amargandhi/claude-buddy-pico/docs/assets/pico-ble-smoke.jpeg

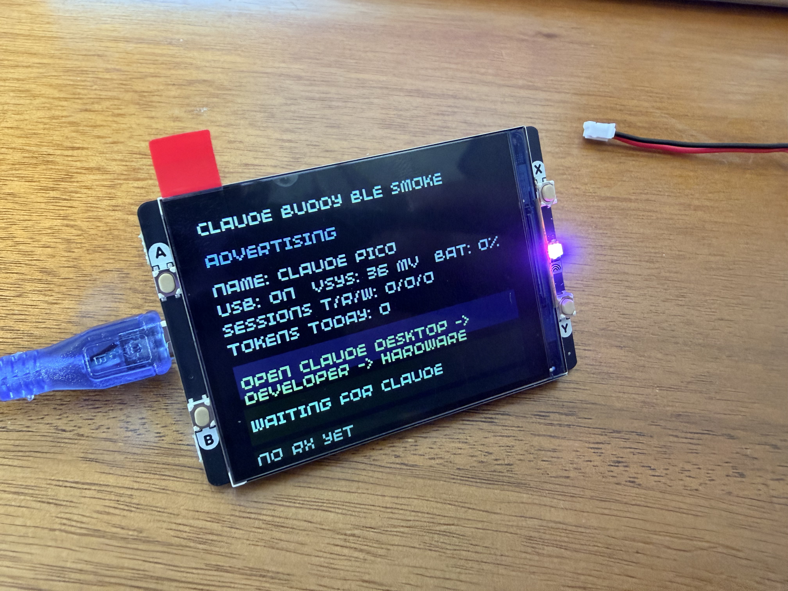
docs/assets/pico-ble-smoke.jpeg
