amargandhi/claude-buddy-pico/docs/assets/readme-gallery-left.jpg

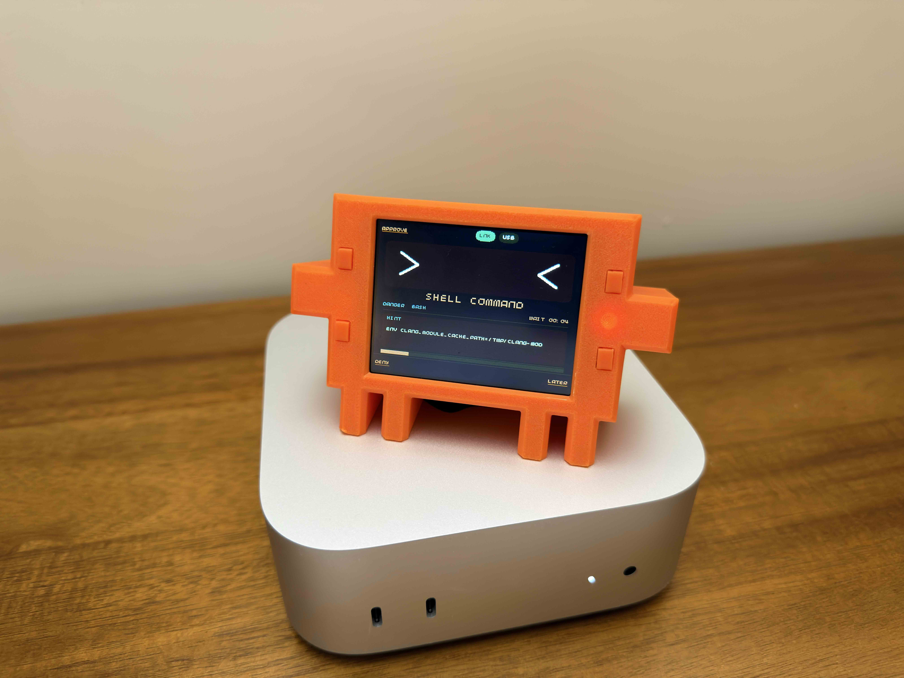
docs/assets/readme-gallery-left.jpg
