amargandhi/claude-buddy-pico/Physical Build/Photos_web/01_hardware/01_02_pico_2w_top.jpg

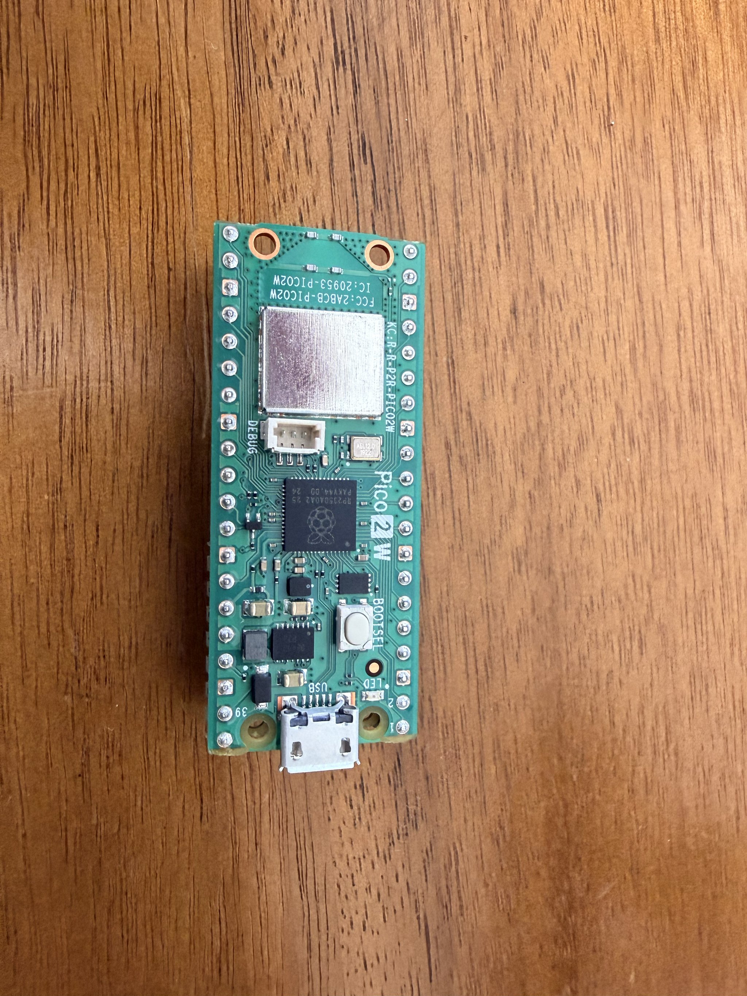
Physical Build/Photos_web/01_hardware/01_02_pico_2w_top.jpg
