amargandhi/claude-buddy-pico/Physical Build/Photos_web/01_hardware/01_04_pico_shim_stack_side.jpg

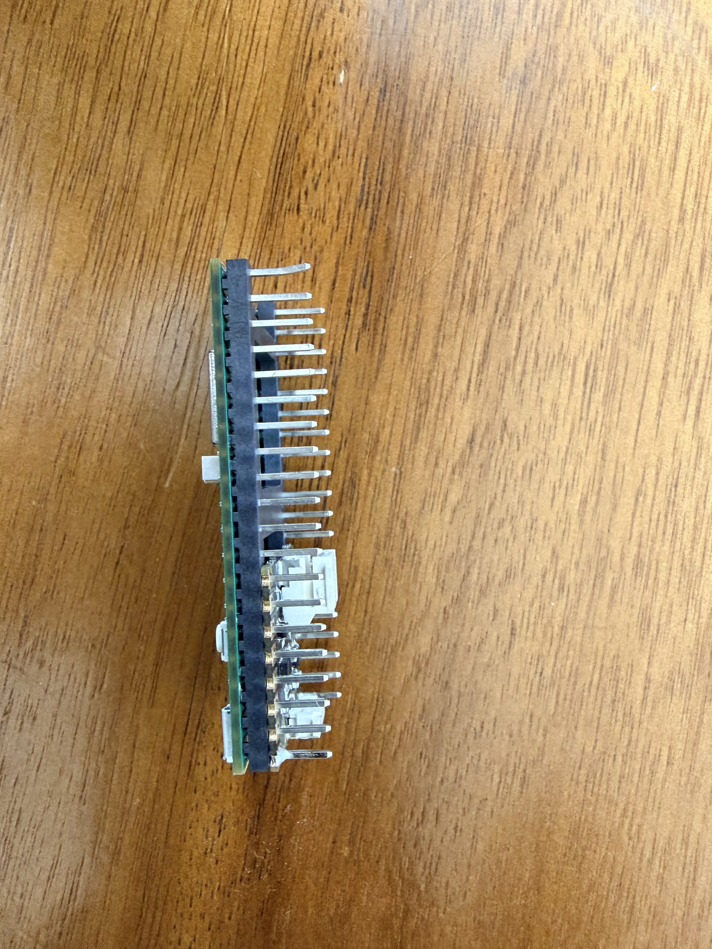
Physical Build/Photos_web/01_hardware/01_04_pico_shim_stack_side.jpg
