amargandhi/claude-buddy-pico/Physical Build/Photos_web/01_hardware/01_06_parts_layout_a.jpg

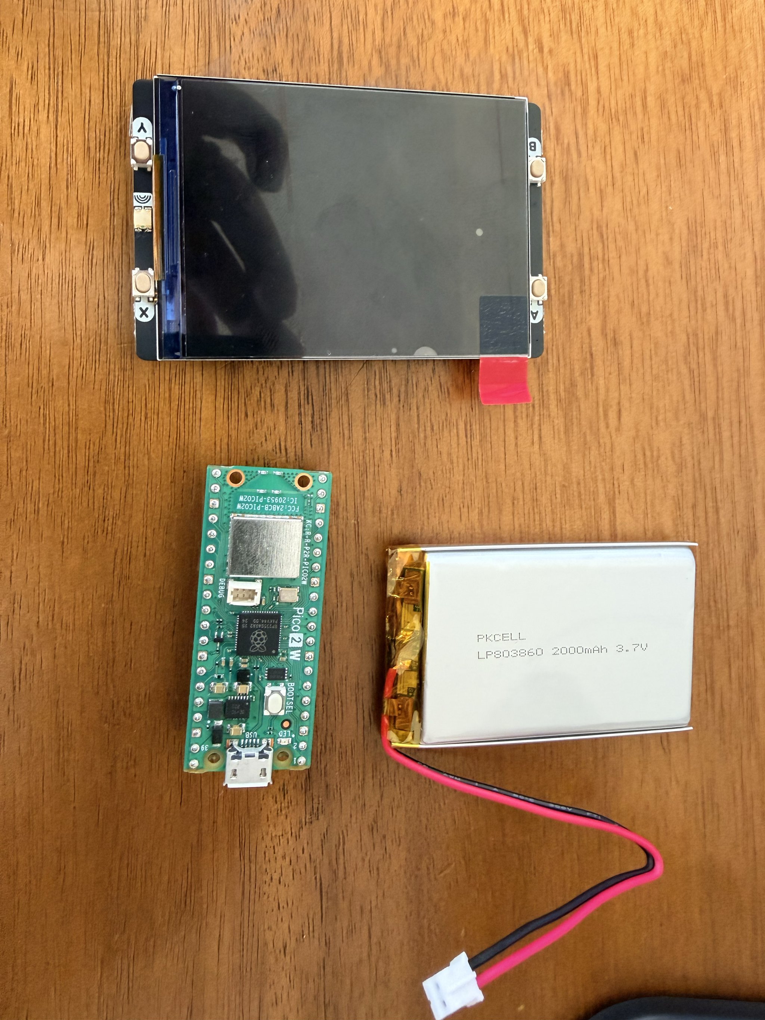
Physical Build/Photos_web/01_hardware/01_06_parts_layout_a.jpg
