amargandhi/claude-buddy-pico/Physical Build/Photos_web/01_hardware/01_08_parts_layout_c.jpg

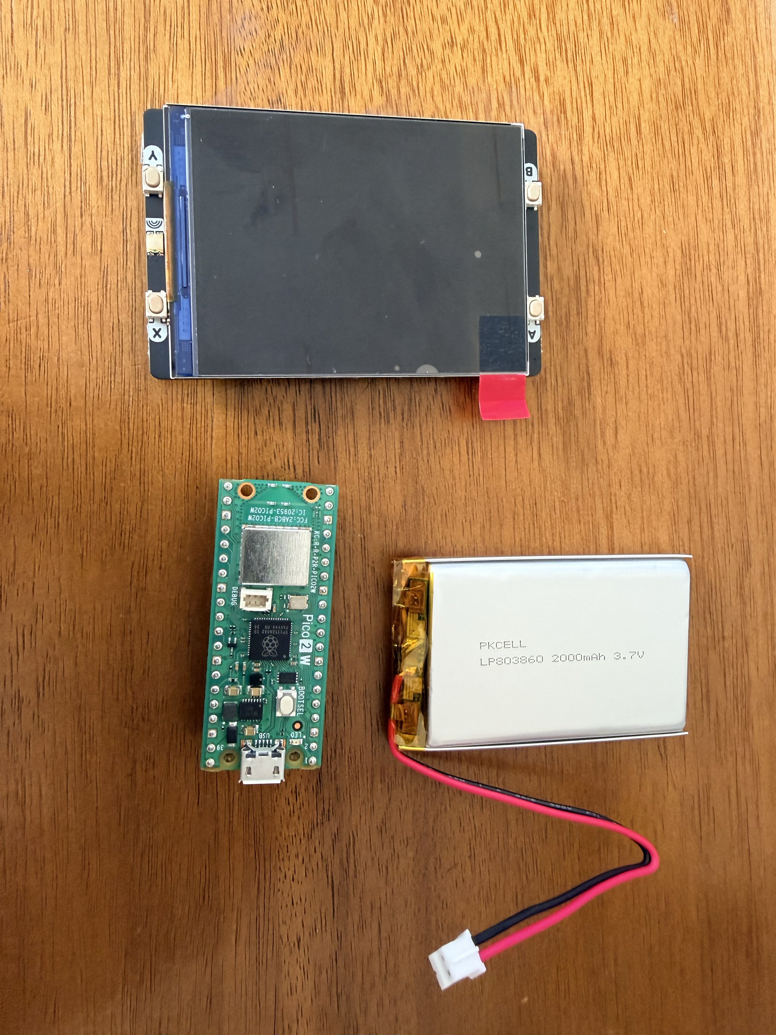
Physical Build/Photos_web/01_hardware/01_08_parts_layout_c.jpg
