amargandhi/claude-buddy-pico/Physical Build/Photos_web/03_assembly/03_02_display_pico_battery_facedown.jpg

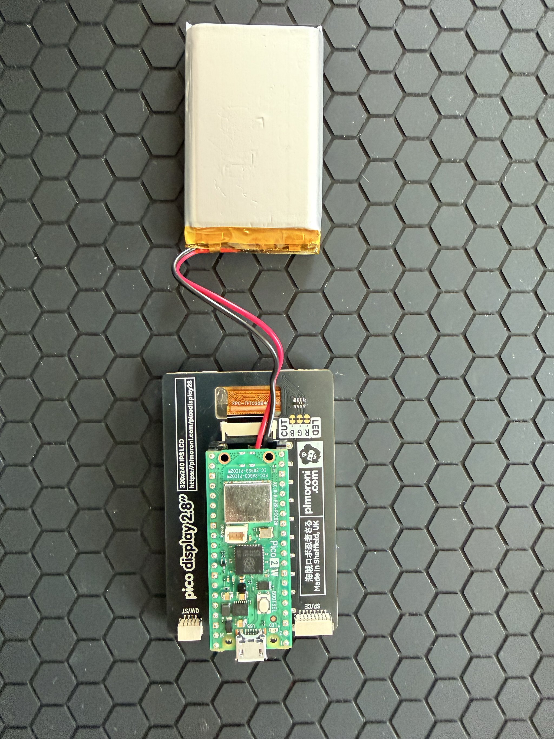
Physical Build/Photos_web/03_assembly/03_02_display_pico_battery_facedown.jpg
