amargandhi/claude-buddy-pico/Physical Build/Photos_web/03_assembly/03_03_pico_display_stack_side.jpg

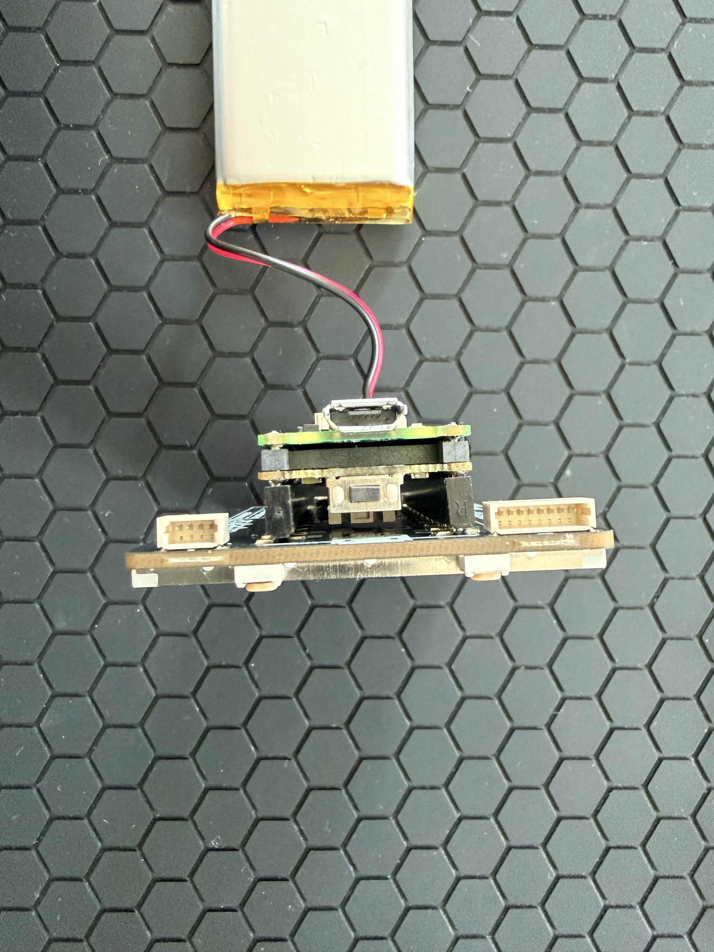
Physical Build/Photos_web/03_assembly/03_03_pico_display_stack_side.jpg
