amargandhi/claude-buddy-pico/Physical Build/Photos_web/03_assembly/03_04_pico_stack_edge_view.jpg

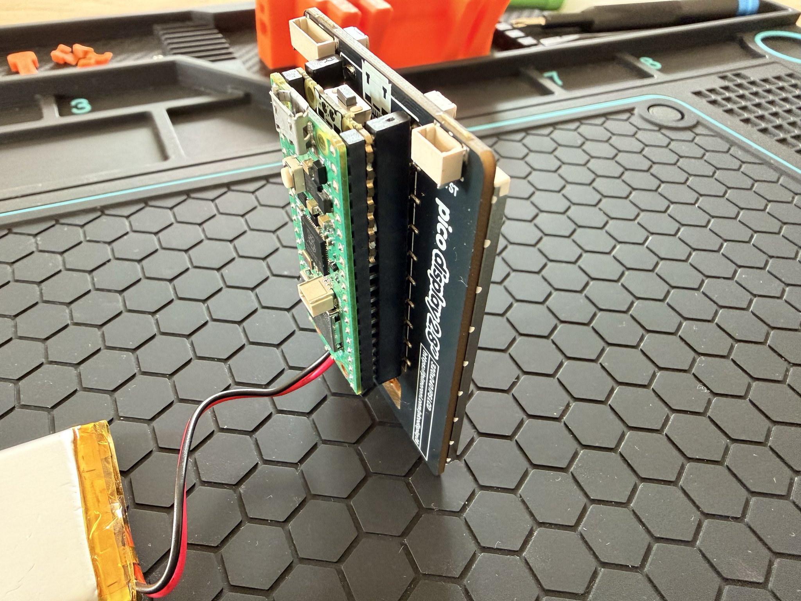
Physical Build/Photos_web/03_assembly/03_04_pico_stack_edge_view.jpg
