amargandhi/claude-buddy-pico/Physical Build/Photos_web/03_assembly/03_05_battery_clip_and_glue.jpg

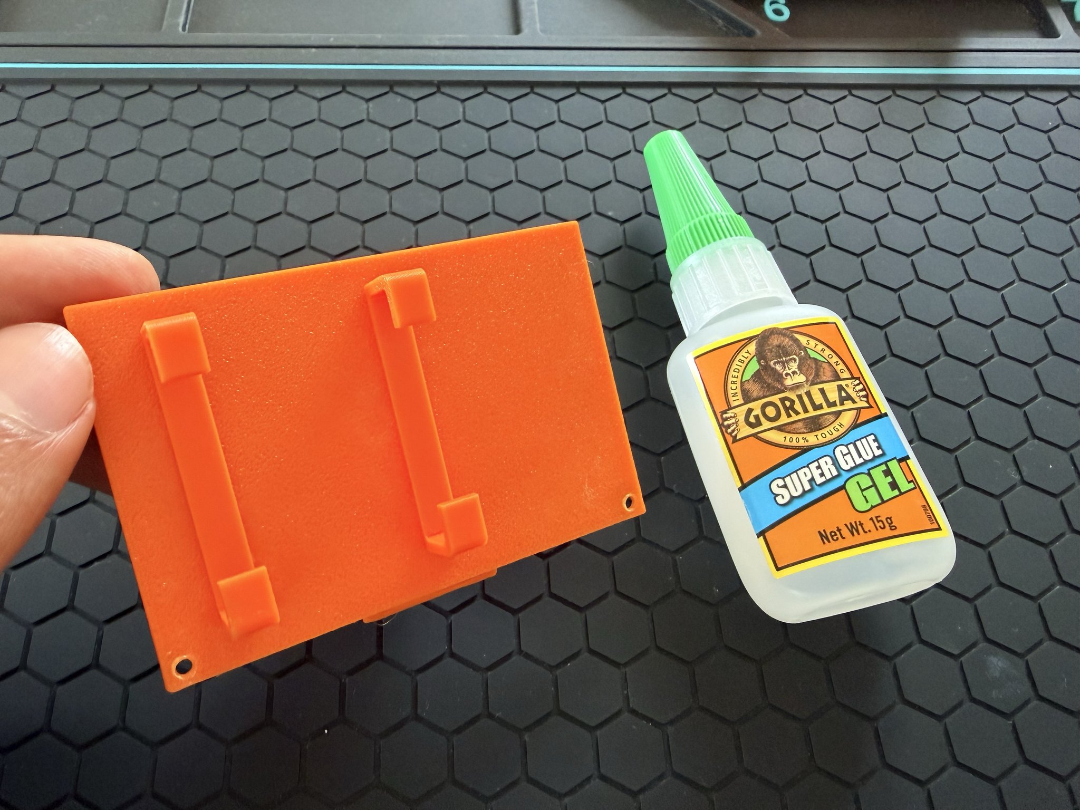
Physical Build/Photos_web/03_assembly/03_05_battery_clip_and_glue.jpg
