amargandhi/claude-buddy-pico/Physical Build/Photos_web/03_assembly/03_09_main_body_empty_angle.jpg

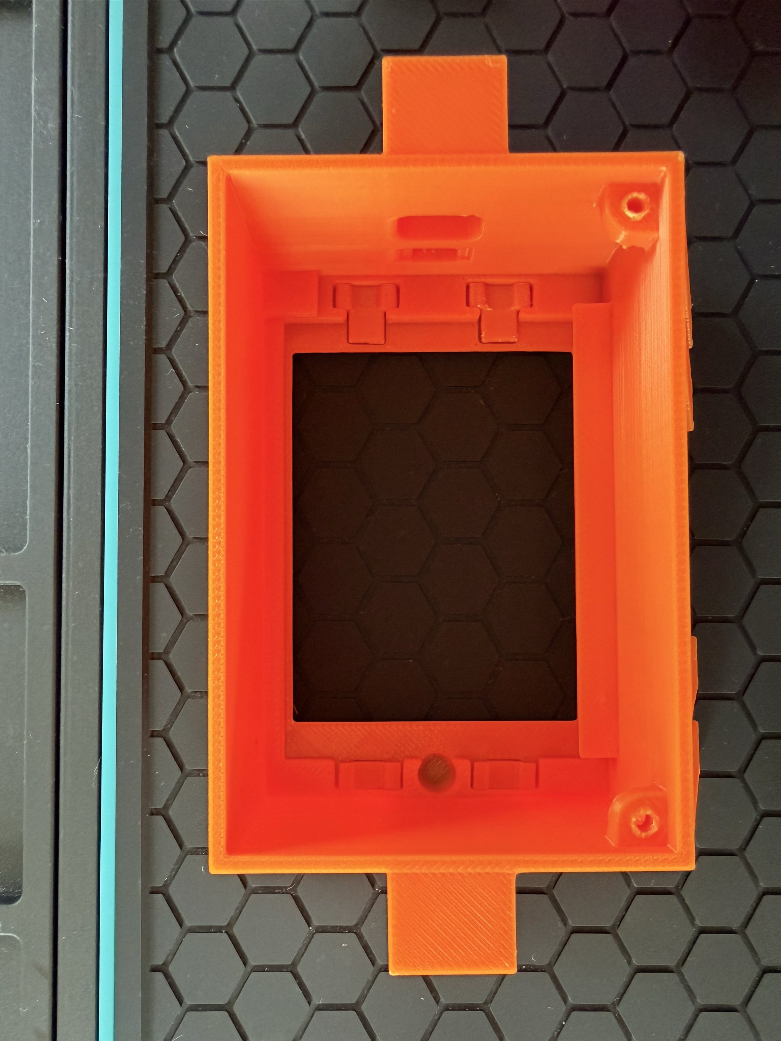
Physical Build/Photos_web/03_assembly/03_09_main_body_empty_angle.jpg
