amargandhi/claude-buddy-pico/Physical Build/Photos_web/03_assembly/03_21_assembled_claude_info_screen.jpg

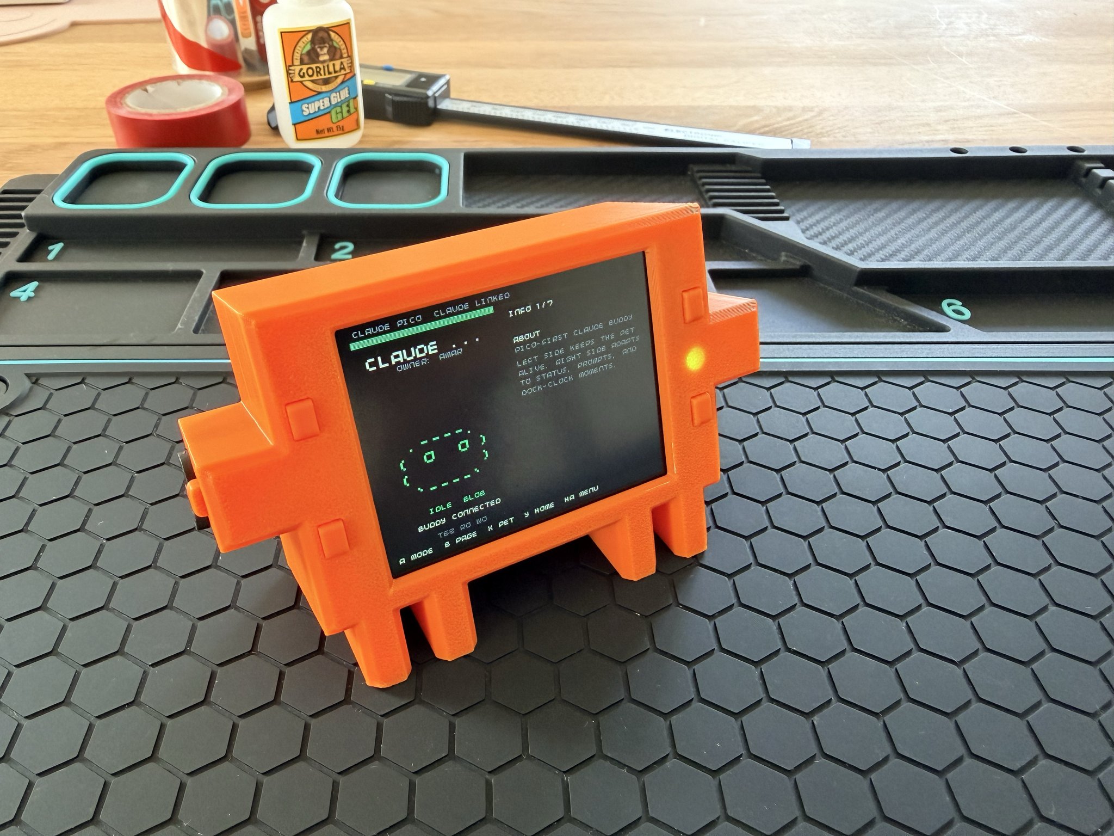
Physical Build/Photos_web/03_assembly/03_21_assembled_claude_info_screen.jpg
