amargandhi/claude-buddy-pico/Physical Build/Photos_web/02_smoke_test/02_02_display_smoke_test_battery_usb.jpg

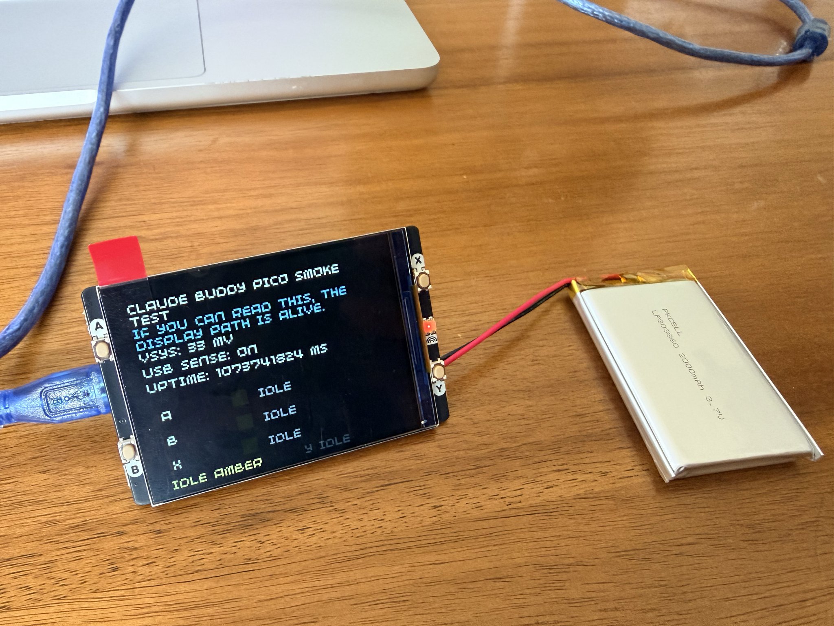
Physical Build/Photos_web/02_smoke_test/02_02_display_smoke_test_battery_usb.jpg
